will-davis/rayglow/hardware/gen_hat_sklib.py

from collections import defaultdict
from skidl import Pin, Part, Alias, SchLib, SKIDL, TEMPLATE

from skidl.pin import pin_types

SKIDL_lib_version = '0.0.1'

gen_hat = SchLib(tool=SKIDL).add_parts(*[
        Part(**{ 'name':'Conn_02x20_Odd_Even', 'dest':TEMPLATE, 'tool':SKIDL, 'aliases':Alias({'Conn_02x20_Odd_Even'}), 'ref_prefix':'J', 'fplist':[''], 'footprint':'Connector_PinSocket_2.54mm:PinSocket_2x20_P2.54mm_Vertical', 'keywords':'connector', 'description':'Generic connector, double row, 02x20, odd/even pin numbering scheme (row 1 odd numbers, row 2 even numbers), script generated (kicad-library-utils/schlib/autogen/connector/)', 'datasheet':'', 'pins':[
            Pin(num='1',name='Pin_1',func=pin_types.PASSIVE,unit=1),
            Pin(num='2',name='Pin_2',func=pin_types.PASSIVE,unit=1),
            Pin(num='3',name='Pin_3',func=pin_types.PASSIVE,unit=1),
            Pin(num='4',name='Pin_4',func=pin_types.PASSIVE,unit=1),
            Pin(num='5',name='Pin_5',func=pin_types.PASSIVE,unit=1),
            Pin(num='6',name='Pin_6',func=pin_types.PASSIVE,unit=1),
            Pin(num='7',name='Pin_7',func=pin_types.PASSIVE,unit=1),
            Pin(num='8',name='Pin_8',func=pin_types.PASSIVE,unit=1),
            Pin(num='9',name='Pin_9',func=pin_types.PASSIVE,unit=1),
            Pin(num='10',name='Pin_10',func=pin_types.PASSIVE,unit=1),
            Pin(num='11',name='Pin_11',func=pin_types.PASSIVE,unit=1),
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
            Pin(num='4',name='Pin_4',func=pin_types.PASSIVE,unit=1),
            Pin(num='5',name='Pin_5',func=pin_types.PASSIVE,unit=1),
            Pin(num='6',name='Pin_6',func=pin_types.PASSIVE,unit=1),
            Pin(num='7',name='Pin_7',func=pin_types.PASSIVE,unit=1),
            Pin(num='8',name='Pin_8',func=pin_types.PASSIVE,unit=1)], 'unit_defs':[] }),
        Part(**{ 'name':'Conn_01x02', 'dest':TEMPLATE, 'tool':SKIDL, 'aliases':Alias({'Conn_01x02'}), 'ref_prefix':'J', 'fplist':[''], 'footprint':'TerminalBlock_Phoenix:TerminalBlock_Phoenix_MKDS-1,5-2-5.08_1x02_P5.08mm_Horizontal', 'keywords':'connector', 'description':'Generic connector, single row, 01x02, script generated (kicad-library-utils/schlib/autogen/connector/)', 'datasheet':'', 'pins':[
            Pin(num='1',name='Pin_1',func=pin_types.PASSIVE,unit=1),
            Pin(num='2',name='Pin_2',func=pin_types.PASSIVE,unit=1)], 'unit_defs':[] }),
        Part(**{ 'name':'74HC245', 'dest':TEMPLATE, 'tool':SKIDL, 'aliases':Alias({'74HC245'}), 'ref_prefix':'U', 'fplist':['', ''], 'footprint':'Package_SO:SOIC-20W_7.5x12.8mm_P1.27mm', 'keywords':'HCMOS BUS 3State', 'description':'Octal BUS Transceivers, 3-State outputs', 'datasheet':'http://www.ti.com/lit/gpn/sn74HC245', 'pins':[
            Pin(num='1',name='A->B',func=pin_types.INPUT,unit=1),
            Pin(num='2',name='A0',func=pin_types.TRISTATE,unit=1),
            Pin(num='3',name='A1',func=pin_types.TRISTATE,unit=1),
            Pin(num='4',name='A2',func=pin_types.TRISTATE,unit=1),
            Pin(num='5',name='A3',func=pin_types.TRISTATE,unit=1),
            Pin(num='6',name='A4',func=pin_types.TRISTATE,unit=1),
            Pin(num='7',name='A5',func=pin_types.TRISTATE,unit=1),
            Pin(num='8',name='A6',func=pin_types.TRISTATE,unit=1),
            Pin(num='9',name='A7',func=pin_types.TRISTATE,unit=1),
            Pin(num='10',name='GND',func=pin_types.PWRIN,unit=1),
            Pin(num='11',name='B7',func=pin_types.TRISTATE,unit=1),
            Pin(num='12',name='B6',func=pin_types.TRISTATE,unit=1),
            Pin(num='13',name='B5',func=pin_types.TRISTATE,unit=1),
            Pin(num='14',name='B4',func=pin_types.TRISTATE,unit=1),
            Pin(num='15',name='B3',func=pin_types.TRISTATE,unit=1),
            Pin(num='16',name='B2',func=pin_types.TRISTATE,unit=1),
            Pin(num='17',name='B1',func=pin_types.TRISTATE,unit=1),
            Pin(num='18',name='B0',func=pin_types.TRISTATE,unit=1),
            Pin(num='19',name='CE',func=pin_types.INPUT,unit=1),
            Pin(num='20',name='VCC',func=pin_types.PWRIN,unit=1)], 'unit_defs':[] }),
        Part(**{ 'name':'R', 'dest':TEMPLATE, 'tool':SKIDL, 'aliases':Alias({'R'}), 'ref_prefix':'R', 'fplist':[''], 'footprint':'Resistor_SMD:R_0805_2012Metric', 'keywords':'R res resistor', 'description':'Resistor', 'datasheet':'', 'pins':[
            Pin(num='1',func=pin_types.PASSIVE,unit=1),
            Pin(num='2',func=pin_types.PASSIVE,unit=1)], 'unit_defs':[] }),
        Part(**{ 'name':'C', 'dest':TEMPLATE, 'tool':SKIDL, 'aliases':Alias({'C'}), 'ref_prefix':'C', 'fplist':[''], 'footprint':'Capacitor_SMD:C_0805_2012Metric', 'keywords':'cap capacitor', 'description':'Unpolarized capacitor', 'datasheet':'', 'pins':[
            Pin(num='1',func=pin_types.PASSIVE,unit=1),
            Pin(num='2',func=pin_types.PASSIVE,unit=1)], 'unit_defs':[] })])
