will-davis/rayglow/rayglow/render/pio_out.py

"""Parallel PIO transport — the default sink, over the 4-lane RP1-PIO bus.

Drop-in for `SpiOut` (the fallback): same `__init__` / `send(bytes)` / `close()`
shape, so the `run_wall` loop and `_SendPipe` use it unchanged. Data + clock are clocked out by
the Pi 5's RP1 PIO via `piobridge/libpioshim.so` (build it first — see
`piobridge/README.md`); READY (and optionally CS) use gpiozero, like SpiOut. The
byte stream is identical to the SPI path, so the firmware/packer don't change —
only the wire. Pairs with firmware bin `phase6-parallel`.

Pin map is the custom HAT's J4 breakout. CS is OFF by default to match the
firmware (`USE_CS=false`): the frame is delimited by READY + the fixed frame size.
Pass `use_cs=True` (and flip the firmware `USE_CS`, jumper GP25) for the CS-framed
reserve. The Pi-side BCM defaults wire to J4 as: GPIO12-15→DATA0-3 (J4.1-4),
GPIO20→DCLK (J4.5), GPIO25←READY (J4.6); CS GPIO21→GP25 jumper when enabled.

The shim is opened lazily on the first `send()` so the frame size (and thus the
DMA buffer) is taken from the actual payload, single- or two-chain alike.
"""
import ctypes
import os

# Per-byte nibble swap (high<->low). The RX shifts left so the FIRST nibble it
# samples becomes the byte's HIGH nibble; the Pi sends low-nibble-first under
# shift-right, so we pre-swap to make the framebuffer byte-identical to the
# packer. bytes.translate applies this 256-entry LUT in C (negligible per frame,
# and on the send worker thread so it overlaps the next render).
_NIBBLE_SWAP = bytes(((b << 4) | (b >> 4)) & 0xFF for b in range(256))


class PioOut:
    _LIB = "libpioshim.so"

    def __init__(self, clkdiv=3.0, ready_bcm=25, nibble_swap=True, use_cs=False,
                 data0_gpio=12, clk_gpio=20, cs_gpio=21, lib_path=None):
        from gpiozero import DigitalInputDevice, DigitalOutputDevice

        path = lib_path or os.path.join(
            os.path.dirname(os.path.abspath(__file__)), "piobridge", self._LIB)
        if not os.path.exists(path):
            raise FileNotFoundError(
                f"{path} not found — build it: `cd {os.path.dirname(path)} && make` "
                f"(see piobridge/README.md)")
        self._lib = ctypes.CDLL(path)
        self._lib.pioshim_open.restype = ctypes.c_void_p
        self._lib.pioshim_open.argtypes = [ctypes.c_uint, ctypes.c_uint,
                                           ctypes.c_uint, ctypes.c_float]
        self._lib.pioshim_send.restype = ctypes.c_int
        self._lib.pioshim_send.argtypes = [ctypes.c_void_p, ctypes.c_char_p,
                                           ctypes.c_uint]
        self._lib.pioshim_close.restype = None
        self._lib.pioshim_close.argtypes = [ctypes.c_void_p]

        self.clkdiv = float(clkdiv)
        self.nibble_swap = bool(nibble_swap)
        self.use_cs = bool(use_cs)
        self.data0_gpio = int(data0_gpio)
        self.clk_gpio = int(clk_gpio)
        self._handle = None

        # READY: RP2350 -> Pi, active high (armed). CS (reserve, off by default):
        # Pi -> RP2350, active low — active_high=False makes cs.on() drive the line
        # LOW (asserted); start deasserted (idle high). Only created when use_cs.
        self.ready = DigitalInputDevice(ready_bcm, pull_up=False)
        self.cs = (DigitalOutputDevice(cs_gpio, active_high=False,
                                       initial_value=False) if self.use_cs else None)
        print(f"pio_out: 4-lane PIO bus — DATA0=GPIO{data0_gpio}, "
              f"CLK=GPIO{clk_gpio}, READY=GPIO{ready_bcm}, "
              f"CS={'GPIO%d' % cs_gpio if self.use_cs else 'off'}, "
              f"clkdiv={self.clkdiv:g}")

    def _ensure_open(self, nbytes):
        if self._handle is not None:
            return
        h = self._lib.pioshim_open(self.data0_gpio, self.clk_gpio,
                                   nbytes, self.clkdiv)
        if not h:
            raise RuntimeError(
                "pioshim_open failed — is /dev/pio0 accessible, piolib built, "
                "and a PIO state machine free?")
        self._handle = h

    def send(self, payload):
        """Wait for READY, (optionally frame with CS), clock the bytes out."""
        self._ensure_open(len(payload))
        if self.nibble_swap:
            payload = payload.translate(_NIBBLE_SWAP)
        self.ready.wait_for_active()        # RP2350 armed its RX DMA
        if self.cs is not None:
            self.cs.on()                    # CS low — frame start
        rc = self._lib.pioshim_send(self._handle, payload, len(payload))
        if self.cs is not None:
            self.cs.off()                   # CS high — frame end
        if rc != 0:
            raise RuntimeError(f"pioshim_send failed ({rc})")

    def close(self):
        try:
            if self._handle is not None:
                self._lib.pioshim_close(self._handle)
                self._handle = None
        finally:
            if self.cs is not None:
                self.cs.close()
            self.ready.close()
